farhad-ekramitalab/LM5141-Synchronous-Buck-Converter/LTSpice/LM5141_AC_Model.asc.asc

B1: bi; I={10.42*V(icmd)}
C1: cap; 15µ
C2: cap; 15µ
C3: cap; 5µ
C4: cap; 5µ
C5: cap; 5µ
C6: cap; 47µ
Ccomp1: cap; 4.7n
Chf1: cap; 180p
G1: g; 1.2m
L2: ind; 1n; Rser=0
L3: ind; 1n; Rser=0
L4: ind; 1n; Rser=0
L5: ind; 1n; Rser=0
L6: ind; 1n; Rser=0
L7: ind; 1n; Rser=0
L9: ind; 2n; Rser=1m
R1: res; 5m
R2: res; 5m
R4: res; 3m
R5: res; 3m
R6: res; 3m
R7: res; 30m
R8: res; 17.4k
R9: res; 10k
R10: res; 1Meg
R11: res; 2.5Meg
Rcomp1: res; 4.7k
Rload: res; 0.66
V4: voltage; 1.2
Vinj: voltage; 0; AC 1
Named nets: 0, SW, Vref, Vfb, comp, comp_mid, out, Vfb_divider, icmd
Murata GRM21BR60J226M Caps
Vishay Flat IHLP4040DZER5R6M01 5.6uH
MLCC CAPS VERY CLOSE TO HIGHSIDE FET 
FOR SMALL LOOP
10uF Murata GRM21BR61E106MA73
Polymer Cap Panasonic 47uF 25SVPD47M
Parasitic
Parasitic
AC ANALYSIS
.ac dec 50 100 10Meg
.op
.plot -V(comp)/V(duty)
