farhad-ekramitalab/LM5141-Synchronous-Buck-Converter/LTSpice/LM5141_Buck.asc

A1: srflop
B1: bv; V=I(L1)*{Rsense}*{Gcs}
B2: bv; V={Vslope*(time-floor(time/Ts)*Ts)/Ts}
B3: bv; V=V(slope)+V(Isense)
B4: bv; V=if(V(q1v)>0.5, 5, 0)
B5: bv; V=if(V(q0v)>0.5, 5, 0)
B6: bv; V=V(PWMH)
B7: bv; V=if((V(PWMH) < 2.5) & (I(L1)>0), 5, 0)
C1: cap; 15µ
C2: cap; 15µ
C3: cap; 5µ
C4: cap; 5µ
C5: cap; 5µ
C6: cap; 47µ
Ccomp: cap; 22n
Chf: cap; 180n
G1: g; 1200µ
HClamp: bi; I=if (V(comp)>0.8, (V(comp)-0.8)/10, 0)
I1: current; PULSE(0 4 3m 1u 1u 2m)
L1: ind; 5.6µ; Rser=1m
L2: ind; 1n; Rser=0
L3: ind; 1n; Rser=0
L4: ind; 1n; Rser=0
L5: ind; 1n; Rser=0
L6: ind; 1n; Rser=0
L7: ind; 1n; Rser=0
L9: ind; 4n; Rser=1m
Lclamp: bi; I=if(V(comp)<0, V(comp)/10, 0)
M1: nmos; CSD17308Q3
M2: nmos; CSD17308Q3
R1: res; 5m
R2: res; 5m
R3: res; 2.5Meg
R4: res; 3m
R5: res; 3m
R6: res; 3m
R7: res; 30m
R8: res; 0.66
R9: res; 17.4k
R10: res; 10k
Rcomp: res; 2.55k
RDC_Rsense: res; 8m
Rdr1: res; 0.1
Rdr: res; 0.1
Rg1: res; 0.1
Rg: res; 0.1
U2: LT1721
V1: voltage; PULSE(12 8 3m 1u 1u 1m 2m)
V3: voltage; 12
V4: voltage; PWL(0 0 500u 1.2)
V5: voltage; PULSE(0 5 0 1n 1n 50n 2.273u)
V6: voltage; 5
Named nets: 0, G-H, G-L, SW, Vref, Vfb, COMP, clk, Isense, slope, SUM, RES, q1v, PWMH, q0v, PWML, out, VIN
.SUBCKT BSC026N08NS5_L0  drain  gate  source
 
Lg     gate  g1    2.2n
Ld     drain d1    100p
Ls     source s1   350p
Rs      s1    s2   412u TC=3m
 
Rg     g1    g2     1.9
M1      d2    g2    s2    s2    DMOS    L=1u   W=1u
.MODEL DMOS NMOS ( KP= 357.9  VTO=4.05  THETA=0  VMAX=1.5e5  ETA=0.0035  LEVEL=3)
Rd     d1    d2    1.46m TC=6m
 
Dbd     s2    d2    Dbt
.MODEL     Dbt    D(BV=85   M=0.75  CJO=1.39n  VJ=2.5V)
Rsp     s2    s3     1.2
Dbd1     s3    d2    Dbt1
.MODEL     Dbt1    D(BV=1000   M=0.75  CJO=5.88n  VJ=2.5V)
Dbody   s2   21    DBODY
.MODEL DBODY  D(IS=49.5p  N=1.12  RS=0.04u  EG=1.12  TT=15n)
Rdiode  d1  21    0.53m TC=1m
 
 
 
 
.MODEL   sw    NMOS(VTO=0  KP=10   LEVEL=1)
Maux      g2   c    a    a   sw
Maux2     b    d    g2    g2   sw
Eaux      c    a    d2    g2   1
Eaux2     d    g2   d2    g2   -1
Cox       b    d2   1.3n
.MODEL     DGD    D(M=0.45   CJO=1.3n   VJ=0.5)
Rpar      b    d2   1Meg
Dgd       a    d2   DGD
Rpar2     d2   a    10Meg
Cgs     g2    s2    5.14n
 
.ENDS  BSC026N08NS5_L0
INFINEON BSC026N08NS5_L0 80V WITH LOW Rdson and high Qg
.tran 8m
40 NS DEAD-TIME IS CONSIDERED (0.261 DUTY INSTEAD OF 0.275 => 5% LOSS) 
OUTPUT VOLTAGE DROPPED TO 3.05 (~5% LOSS)
.meas Pin AVG -V(VIN)*I(V3) FROM 5m TO 6m
 
.meas Pout AVG V(out)*I(R8) FROM 5m TO 6m
 
.meas Eff PARAM Pout/Pin
.step param I 1 5 1
Murata GRM21BR60J226M Caps
Vishay Flat IHLP4040DZER5R6M01 5.6uH
MLCC CAPS VERY CLOSE TO HIGHSIDE FET 
FOR SMALL LOOP
10uF Murata GRM21BR61E106MA73
Polymer Cap Panasonic 47uF 25SVPD47M
Parasitic
Parasitic
Parasitic
Parasitic
.param Rsense=8m
.param Gcs=12
.param Fsw=440k
.param Ts={1/Fsw}
.param Vslope=65m
SLOPE COMPENSATION
PWM GENERATOR
440KHZ SWITCHING FREQ FOR CLOCK
CLAMP ON COMP 
WILL LIMIT THE MAX CURRENT OF INDUCTOR
ILpeak = Vcomp / 0.096
0.8/0.096= 8.3A max
LOAD STEP
LINE STEP
THIS RAMP IS CONSISTENT WITH
 THE SOFT START OF LM5141
DIODE EMULATION MODEL
* SUBCKT Definition:  1=D  2=G  3=S
**********************************************************************
.SUBCKT CSD17308Q3  1 2 3
.PARAM  ptrc1   3.10e-3  
.PARAM  ptrc2   9.5e-6
.PARAM  pwidthP 0.6120192
.PARAM  pwidth  {pwidthP*1e6}
.PARAM  perimP  {2.1*pwidthP}
.PARAM  perim   {perimP*1e6}
*pkgL = logical value:  0 for Si Die ONLY;  1 for packaged part.
.PARAM  pkgL    1.0
M1   10 11 12 12  NMOS W={pwidthP} L=0.5u  PD={perimP}  PS={perimP}
DBD   8  7         DBD
RDB   8  7   1e10
CGD0  5  7              {pkgL*1E-12 + 1e-14}
CGS0  5  8                {pkgL*2e-12 + 1e-14}
CDS0 10 12                {pkgL*5e-12 + 1e-14}
M2   12 11 12 20  PMOSd W={pwidthP} L=0.103u  PD={perimP}  PS={perimP}
DDx  20 10   DDx
DDG  14  5   DD
DGD  14 10   DD
* Note:  gate oxide capacitance included in NMOS below
CGS   5 13            72E-12
RGS  13  8              190
LGG   2  5                 {pkgL*0.95e-9 + 0.1e-9}
RGG   5 11             {pkgL*0.25 + 0.8}
RSB  12  9   RTEMP 0.90E-3
RSS   9  8       0.04e-3
RSP   8  6             {pkgL*0.50e-3 + 0.02e-3}
LSS   6  3            {pkgL*0.51E-9 + 0.02e-9}
RSL   6  3   2.5
RDP   4  7          {pkgL*0.65e-3 + 0.05e-3}
RDD   7 10            RTEMP 3.69e-3
LDD   1  4       0.05E-9
******************************************************************* 
.MODEL  NMOS   NMOS (    LEVEL  = 7             Version = 3.2
+ TNOM   = 27            LINT   = 0.055e-6      CAPMOD = 2
+ TOX    = 1.75e-8       NCH    = 1.598e17      NSUB   = 1.0e16
+ AGS    = 0.0           PVAG   = 0.2
+ A0     = 1.10          A1     = 0.0           A2     = 0.9
+ UA     = 1.30e-9       UB     = 3.0e-18       VBM    = -5.0
+ UA1    = 2.4e-9        UB1    = -3.5e-18      UTE    = -1.50
+ KT1    = -0.64         KT2    = 0.022         KT1L   = 1.0e-12
+ DVT0   = 2.5           DVT1   = 0.62              DVT2   = -0.033
+ ETA0   = 0.045         ETAB   = -0.07         XJ     = 4e-7
+ PDIBLC1= 0.08          PDIBLC2= 0.025         NLX    = 1.78e-7
+ PSCBE1 = 6.0e8         PSCBE2 = 1e-7          PCLM   = 1.3
+ VOFF   = -0.235        NFACTOR= 1.4           JS     = 0
+ DROUT  = 1.10          DSUB   = 1.3           DELTA  = 0.01
+ CJ     = 1e-18         CJSW   = 1e-18         CF     = 0
+ CGSO   = 161e-12       CGDO   = 21e-12        CGBO   = 0    )
******************************************************************* 
.MODEL  PMOSd   PMOS (   LEVEL  = 1
+ TNOM   = 27            VTO    = -0.3                 IS     = 6.0e-14
+ TOX    = 1.75e-8       NSUB   = 2e18
+ CJ     = 1e-18         CJSW   = 1e-18
+ CGSO   = 1e-18         CGDO   = 1e-18         CGBO   = 1e-18 )
******************************************************************* 
.MODEL DBD D (CJO=1100e-12 VJ=1.0 M=0.525 FC=0.5 TT=2e-09 TNOM=27
+ IS=1.1e-12 N=1.01 RS=3.0e-3 TRS1=3.3e-3 XTI=2.8 BV=33)
.MODEL DDx D (CJO=20e-12 VJ=0.40 M=0.50 IS=1e-12 RS=0.1 TNOM=27)
.MODEL DD  D (CJO=205e-12 VJ=0.40 M=0.838 IS=1e-13 RS=1 TNOM=27 BV=31)
******************************************************************* 
.MODEL RTEMP RES (TC1={ptrc1} TC2={ptrc2})
*******************************************************************
.ENDS CSD17308Q3
*$
TI CSD17308Q3 MODEL WITH LOW Qg and moderate Rdson
EFFICIENCY FOR TI MOS VS INFINEON MOS
 
TI MOS ==> 0.96 FOR 5A
                    0.93 FOR 0.5A
 
INFINEON ==> 0.93 FOR 5A
                          0.79 FOR 0.5A
